edgarkech/scalable_field_camera/pictures/first_prototype/fomapan_200_4x5_2020-04-05-0008.jpg

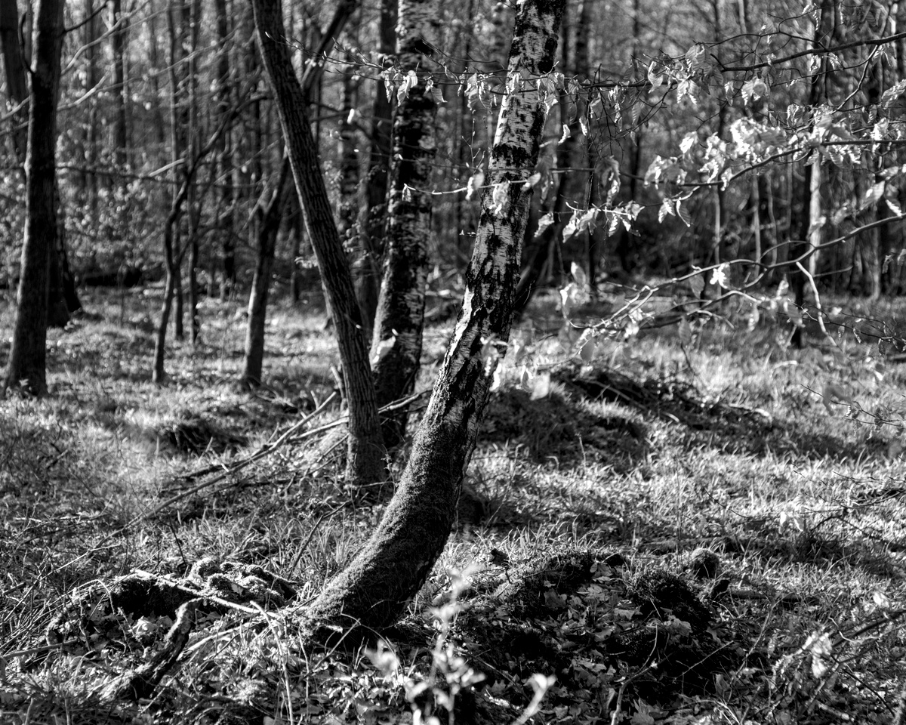
pictures/first_prototype/fomapan_200_4x5_2020-04-05-0008.jpg
