edgarkech/scalable_field_camera/pictures/first_prototype/MVIMG_20200405_085028_163_01.jpg

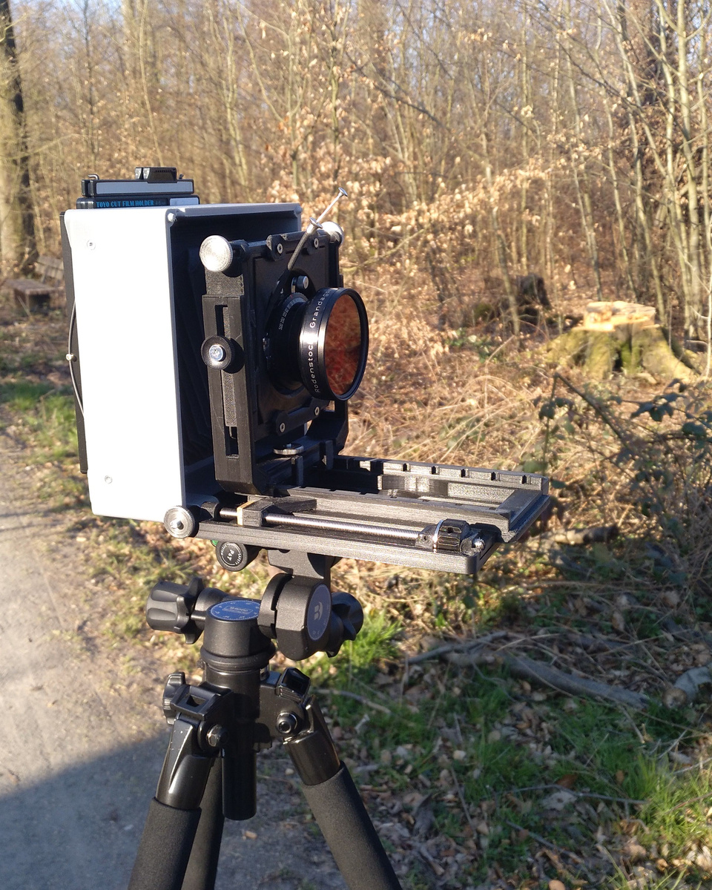
pictures/first_prototype/MVIMG_20200405_085028_163_01.jpg
