edgarkech/scalable_field_camera/pictures/first_prototype/MVIMG_20200405_091932_636.jpg

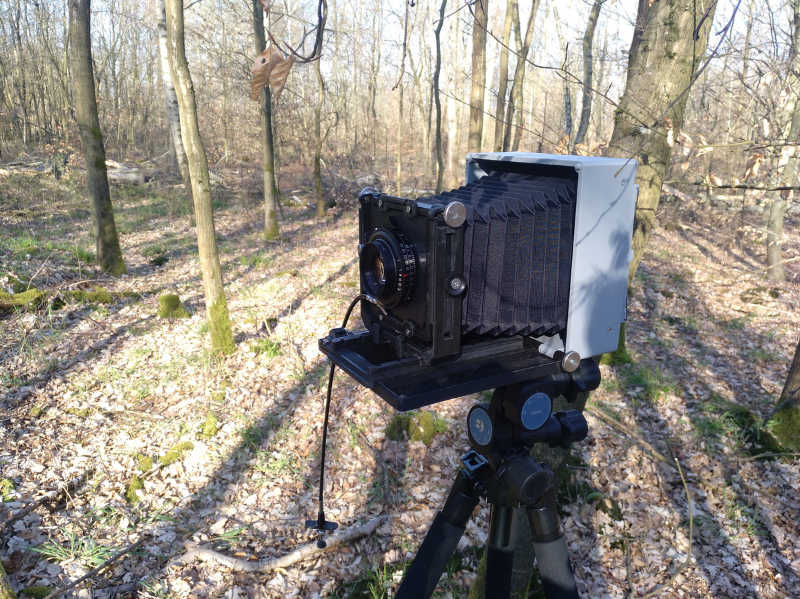
pictures/first_prototype/MVIMG_20200405_091932_636.jpg
