edgarkech/scalable_field_camera/pictures/version_1.0/IMG_20250819_194735843_HDR.jpg

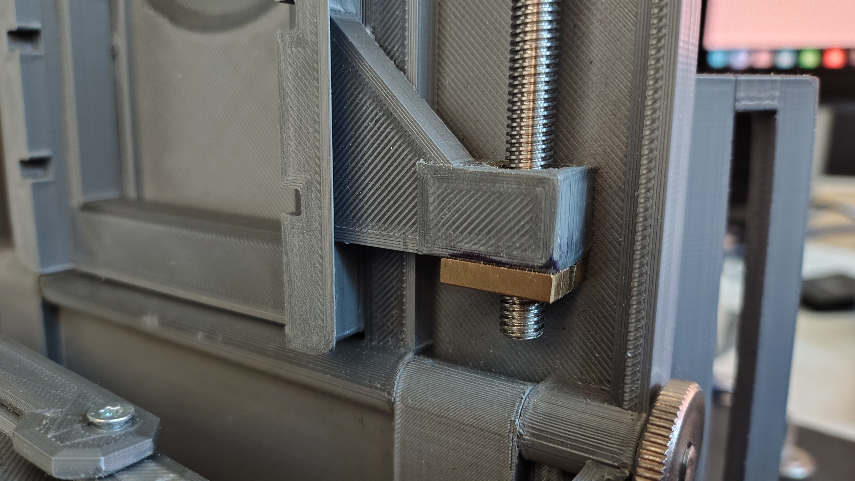
pictures/version_1.0/IMG_20250819_194735843_HDR.jpg
