edgarkech/scalable_field_camera/pictures/version_1.0/IMG_20250819_194852616_HDR.jpg

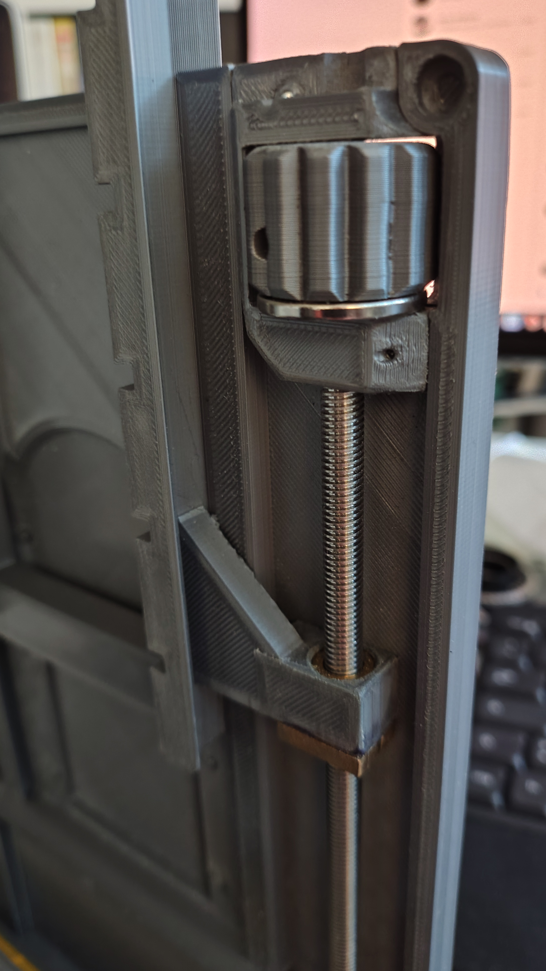
pictures/version_1.0/IMG_20250819_194852616_HDR.jpg
