edgarkech/scalable_field_camera/pictures/version_1.0/XT203508.jpg

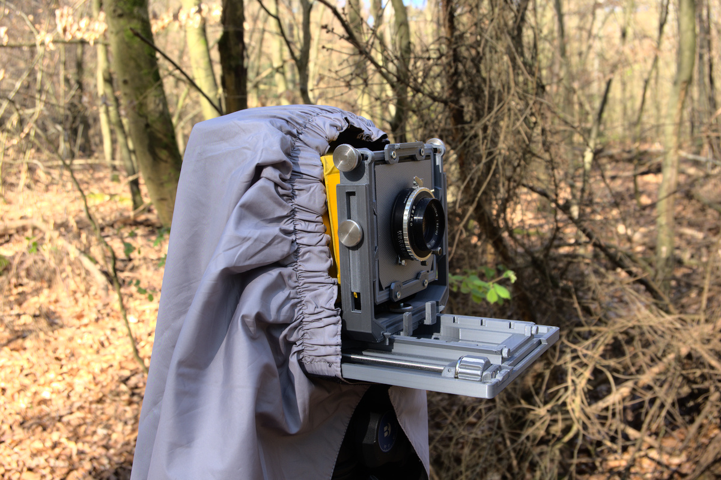
pictures/version_1.0/XT203508.jpg
