edgarkech/scalable_field_camera/pictures/version_1.0/XT203509.jpg

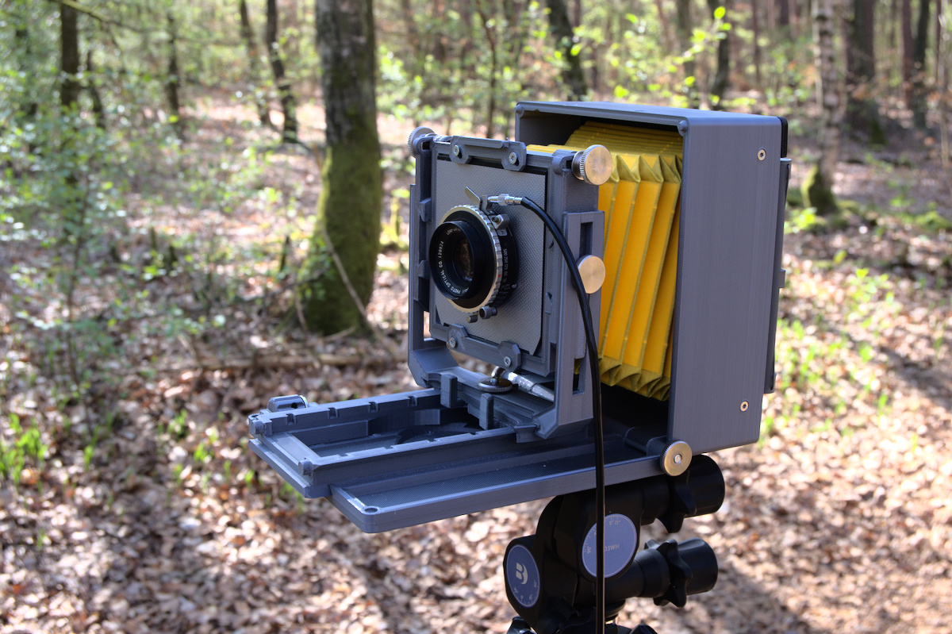
pictures/version_1.0/XT203509.jpg
