edgarkech/scalable_field_camera/pictures/version_1.0/XT203510.jpg

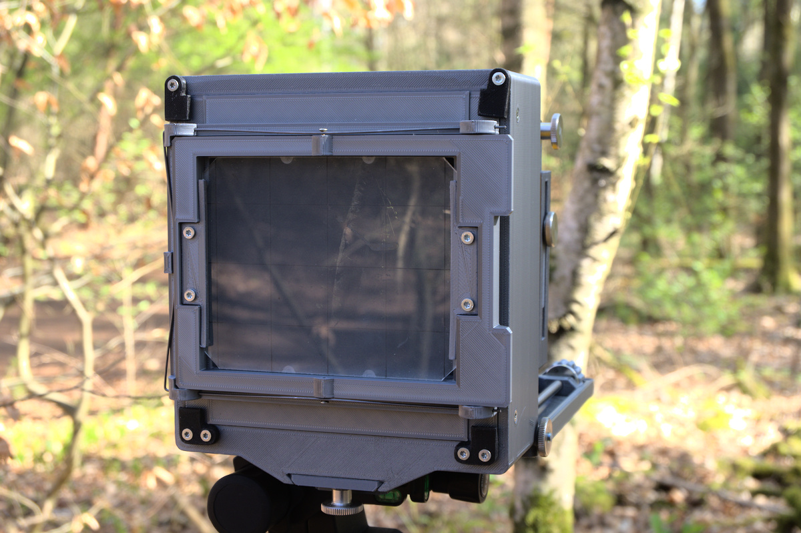
pictures/version_1.0/XT203510.jpg
