edgarkech/scalable_field_camera/pictures/XT203534.jpg

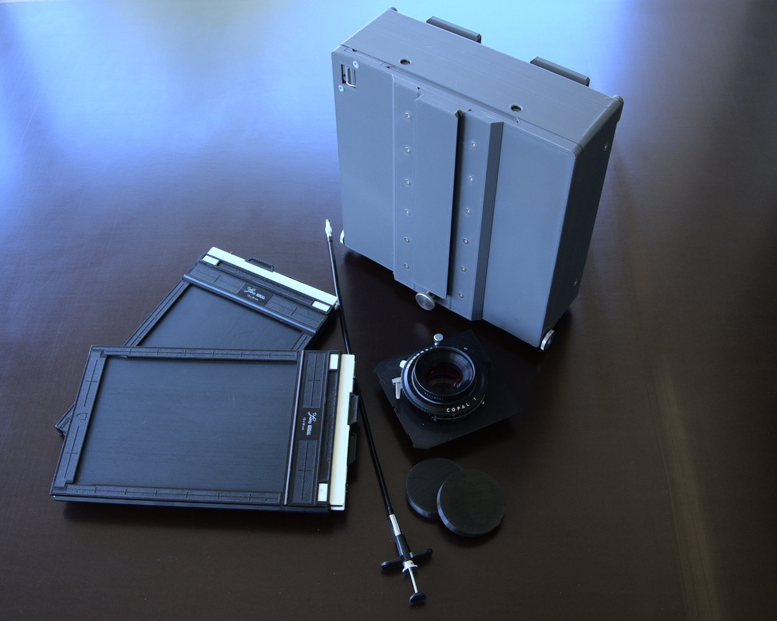
pictures/XT203534.jpg
