edgarkech/scalable_field_camera/pictures/XT203535.jpg

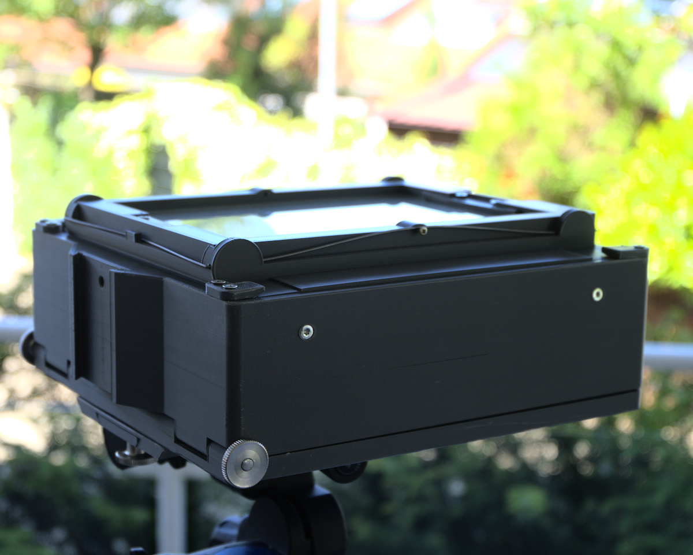
pictures/XT203535.jpg
