edgarkech/scalable_field_camera/pictures/XT203537.jpg

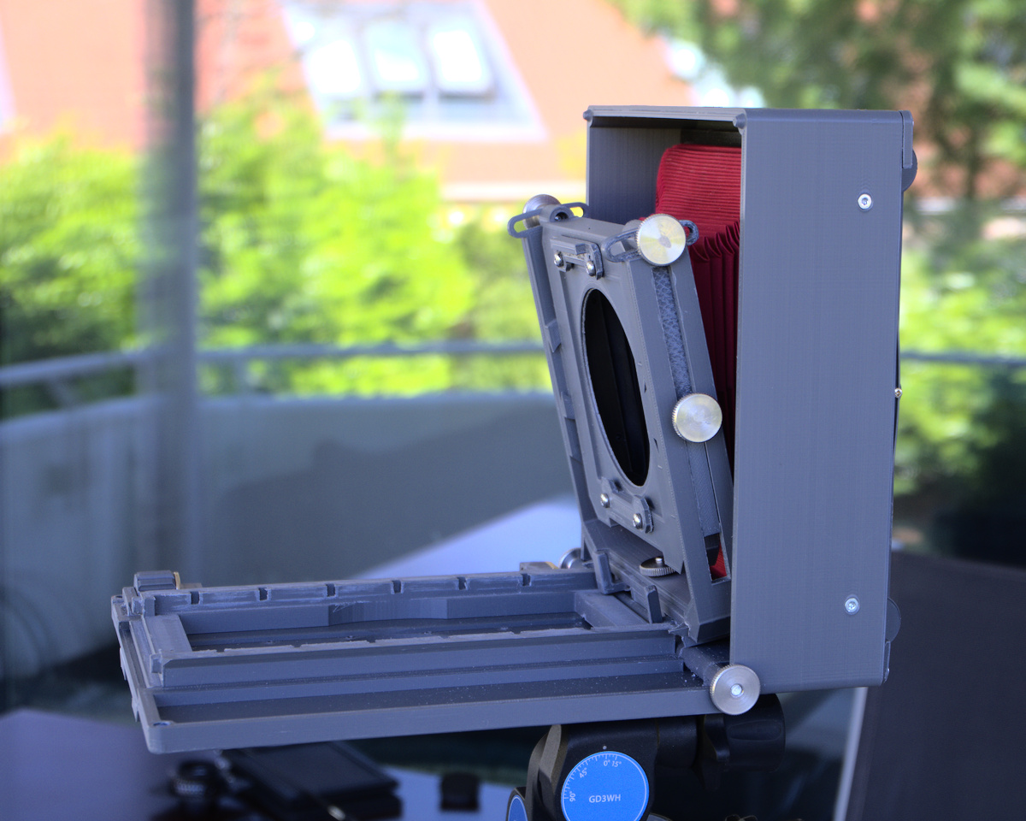
pictures/XT203537.jpg
