edgarkech/scalable_field_camera/pictures/XT203543.jpg

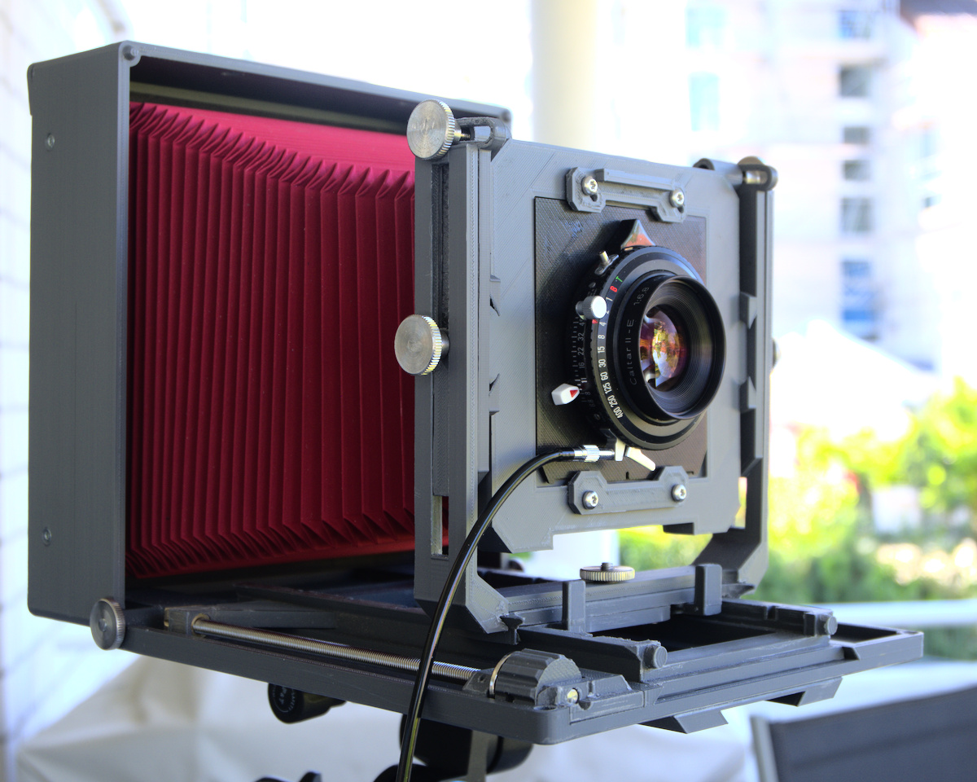
pictures/XT203543.jpg
