edgarkech/scalable_field_camera/pictures/XT203546.jpg

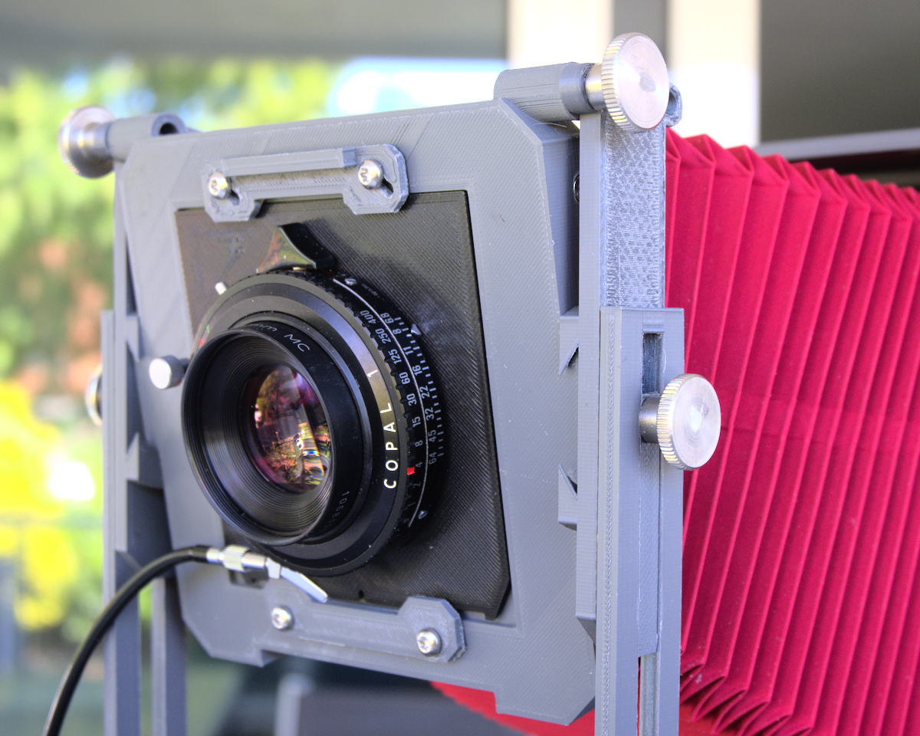
pictures/XT203546.jpg
