edgarkech/scalable_field_camera/STL_4x5/front_standard_tilt_plate.stl

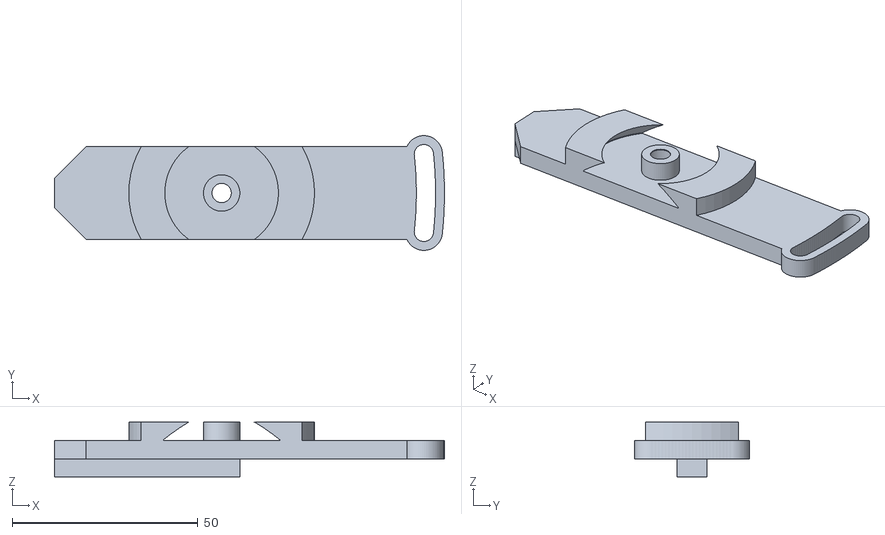
[picture p39: CAD file, 2020-03-26]
STL_4x5/front_standard_tilt_plate.stl
105.0 x 30.9 x 14.8
