edgarkech/scalable_field_camera/STL_5x7/slider.stl

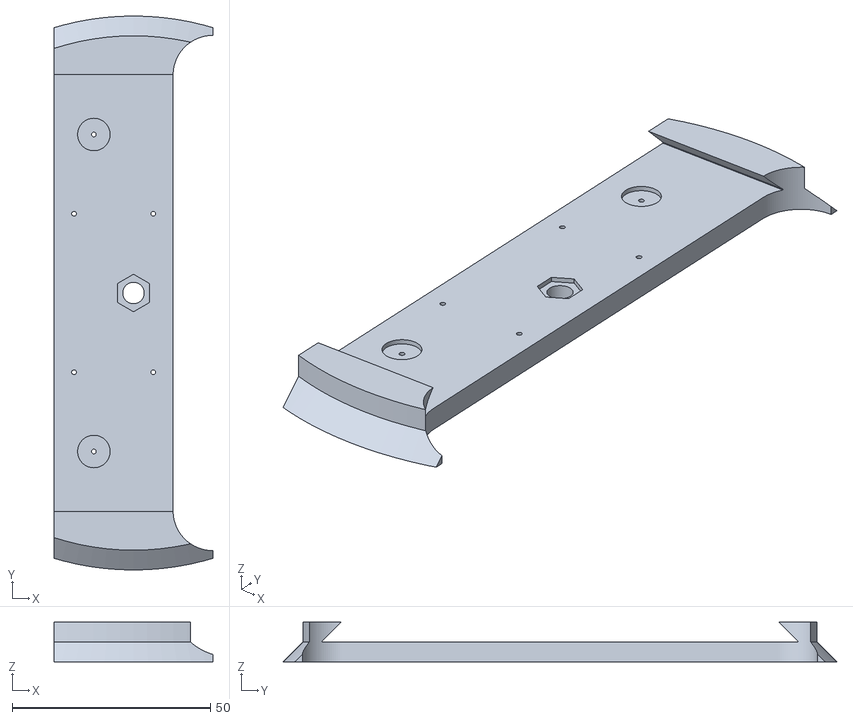
[picture p40: CAD file, 2020-05-10]
STL_5x7/slider.stl
40.0 x 139.8 x 10.0
