edgarkech/scalable_field_camera/STL_4x5/back_plate.stl

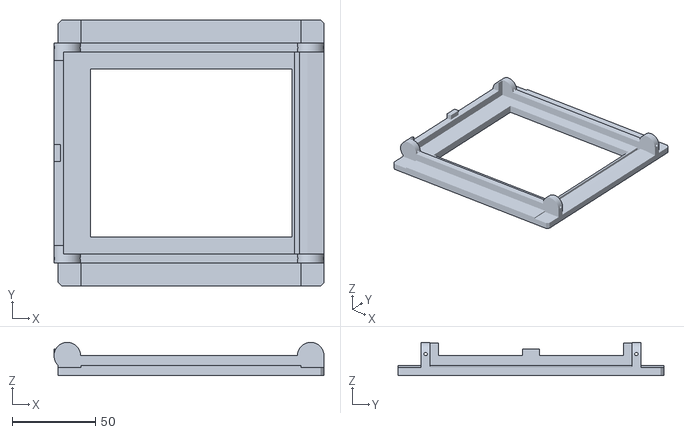
[picture p41: CAD file, 2020-03-26]
STL_4x5/back_plate.stl
162.1 x 159.6 x 20.0
