edgarkech/scalable_field_camera/STL_5x7/pulling_lever.stl

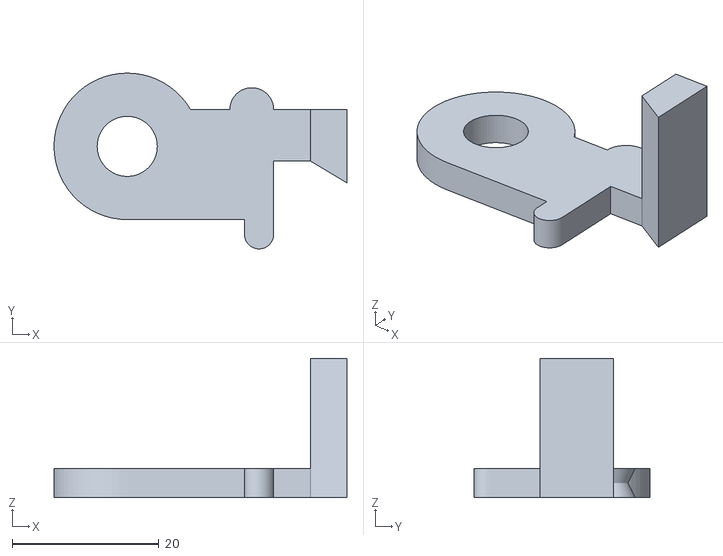
[picture p42: CAD file, 2020-05-10]
STL_5x7/pulling_lever.stl
40.0 x 24.0 x 19.0
