edgarkech/scalable_field_camera/STL_4x5/lensboard_carrier.stl

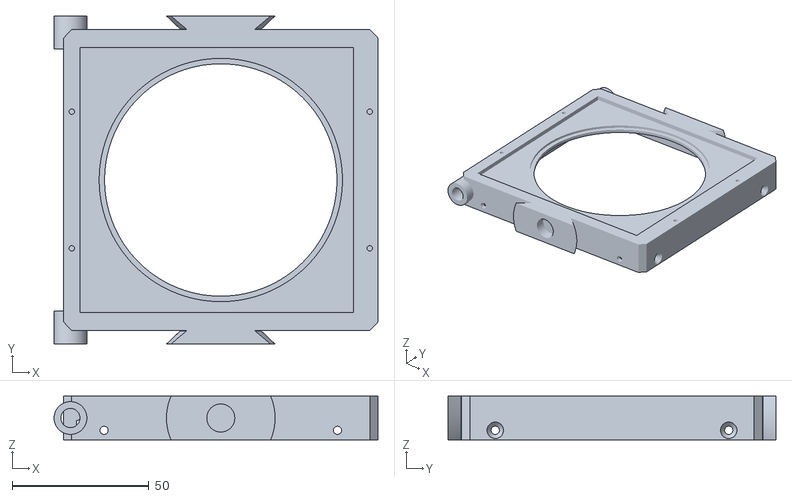
[picture p43: CAD file, 2020-03-26]
STL_4x5/lensboard_carrier.stl
118.5 x 120.0 x 16.0
