edgarkech/scalable_field_camera/STL_5x7/lensboard_carrier.stl

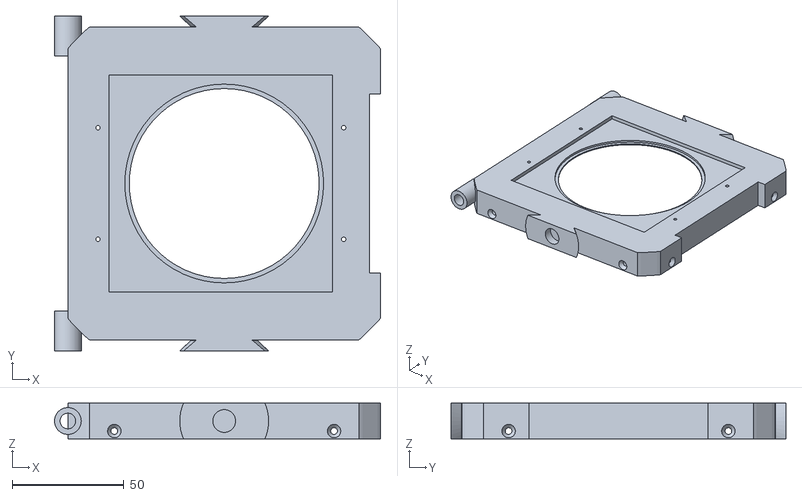
[picture p44: CAD file, 2020-05-10]
STL_5x7/lensboard_carrier.stl
146.0 x 150.0 x 16.0
