edgarkech/scalable_field_camera/STL_4x5/front_standard.stl

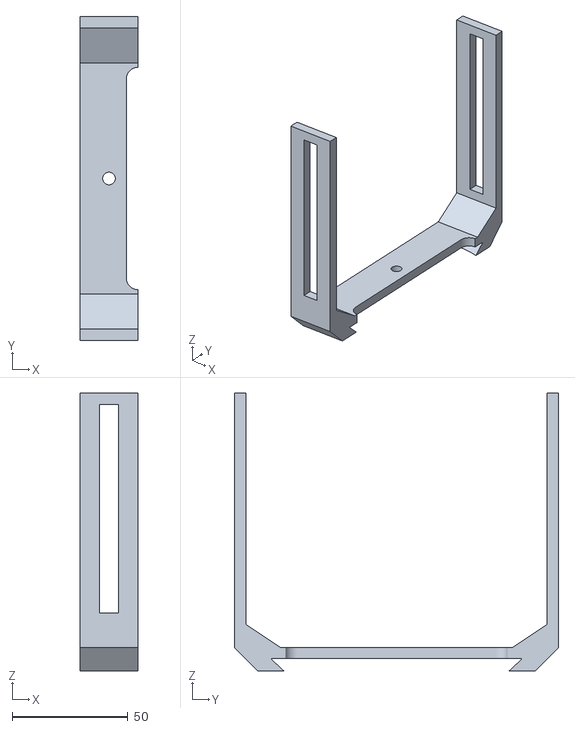
[picture p45: CAD file, 2020-03-26]
STL_4x5/front_standard.stl
25.0 x 140.0 x 120.0
