edgarkech/scalable_field_camera/STL_5x7/front_lid_dovetail.stl

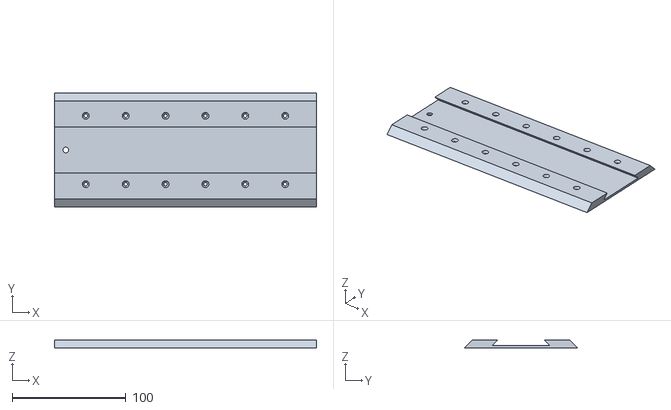
[picture p46: CAD file, 2020-05-06]
STL_5x7/front_lid_dovetail.stl
230.0 x 100.0 x 7.00
