edgarkech/scalable_field_camera/STL_4x5/ground_glass_frame.stl

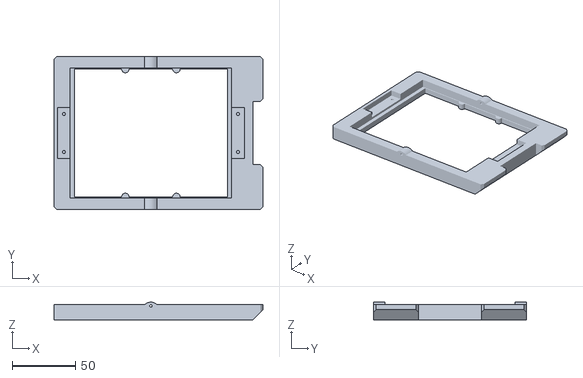
[picture p47: CAD file, 2020-03-26]
STL_4x5/ground_glass_frame.stl
165.0 x 120.5 x 14.0
