edgarkech/scalable_field_camera/STL_5x7/tripod_plate.stl

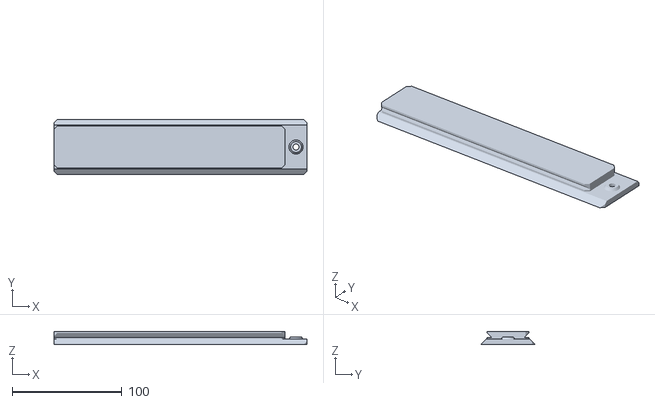
[picture p48: CAD file, 2020-05-06]
STL_5x7/tripod_plate.stl
230.0 x 49.8 x 12.0
