edgarkech/scalable_field_camera/STL_4x5/front_lid_dovetail.stl

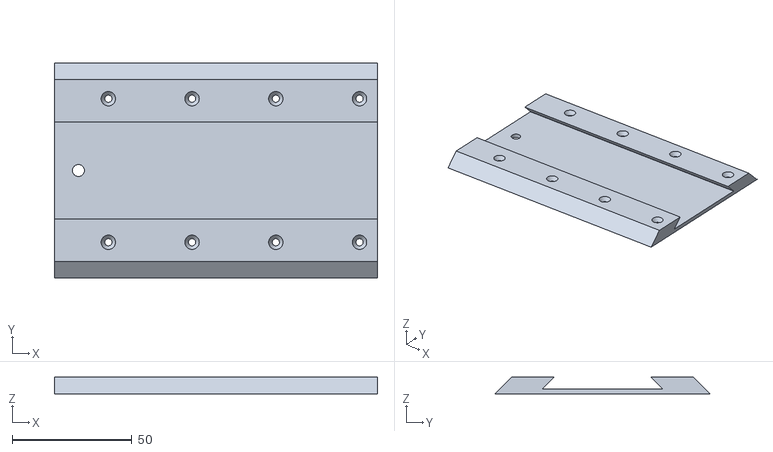
[picture p49: CAD file, 2020-03-26]
STL_4x5/front_lid_dovetail.stl
135.0 x 90.0 x 7.00
