edgarkech/scalable_field_camera/STL_5x7/ground_glass_frame.stl

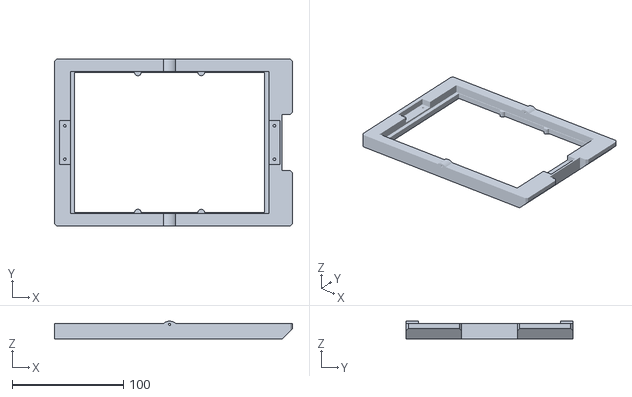
[picture p50: CAD file, 2020-05-06]
STL_5x7/ground_glass_frame.stl
214.0 x 150.0 x 16.0
