edgarkech/scalable_field_camera/STL_5x7/front_lid.stl

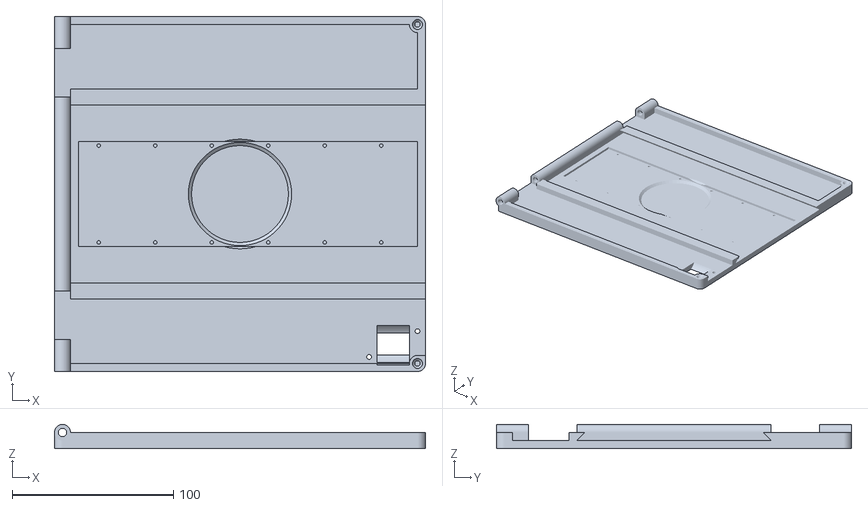
[picture p51: CAD file, 2020-04-23]
STL_5x7/front_lid.stl
230.0 x 220.0 x 15.0
