edgarkech/scalable_field_camera/STL_4x5/slider.stl

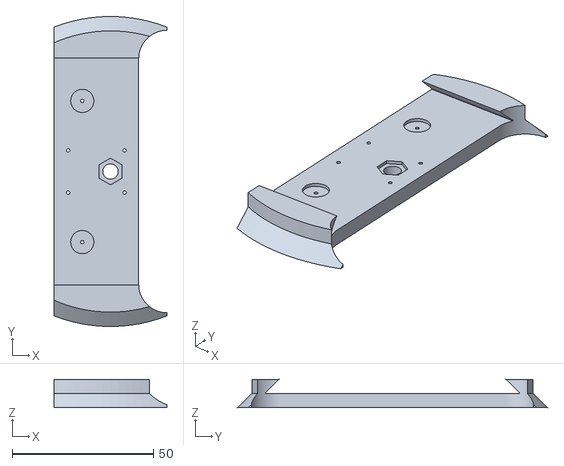
[picture p52: CAD file, 2020-03-26]
STL_4x5/slider.stl
40.0 x 109.8 x 10.0
