edgarkech/scalable_field_camera/STL_5x7/rails.stl

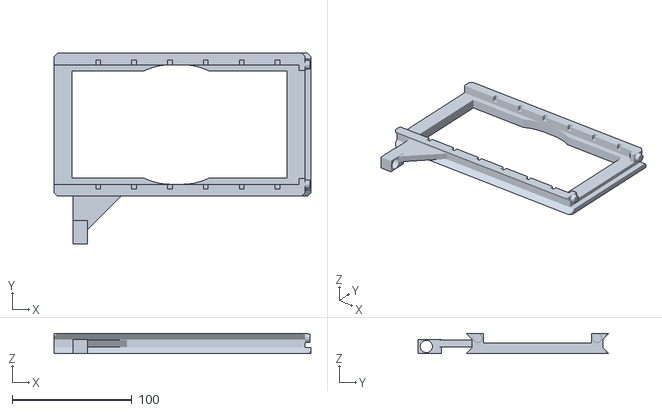
[picture p53: CAD file, 2020-04-23]
STL_5x7/rails.stl
215.0 x 159.9 x 17.0
