edgarkech/scalable_field_camera/STL_5x7/body.stl

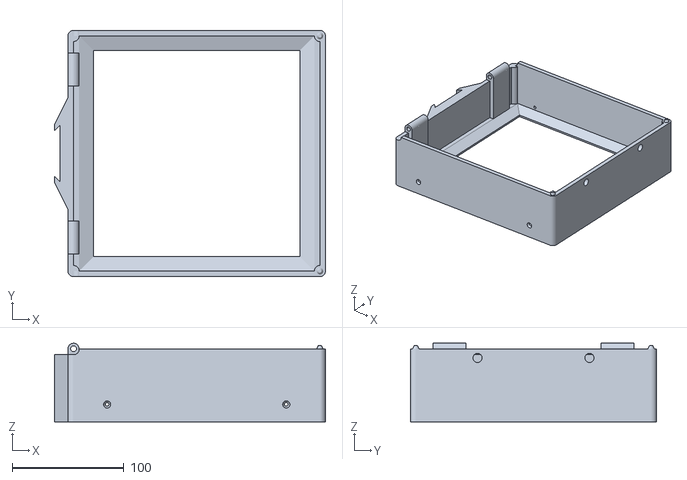
[picture p54: CAD file, 2020-04-23]
STL_5x7/body.stl
242.0 x 220.0 x 70.2
