edgarkech/scalable_field_camera/STL_5x7/bellows_front_frame.stl

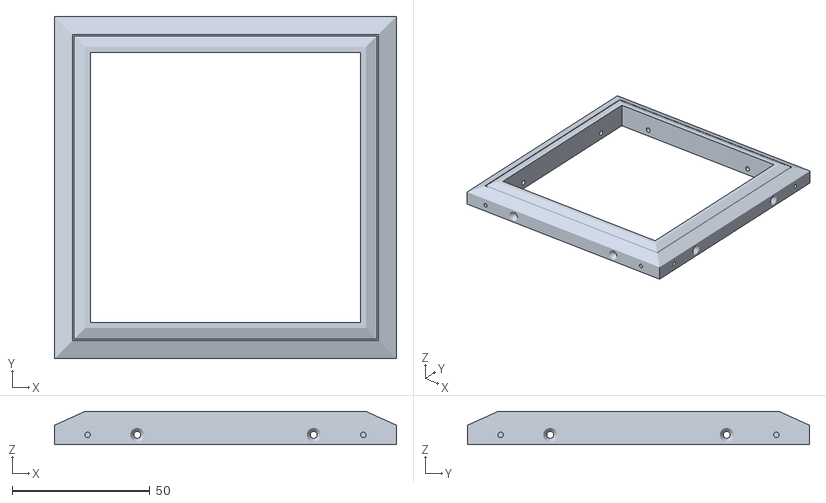
[picture p55: CAD file, 2020-04-22]
STL_5x7/bellows_front_frame.stl
124.0 x 124.0 x 12.0
