edgarkech/scalable_field_camera/STL_5x7/bellows_back_frame.stl

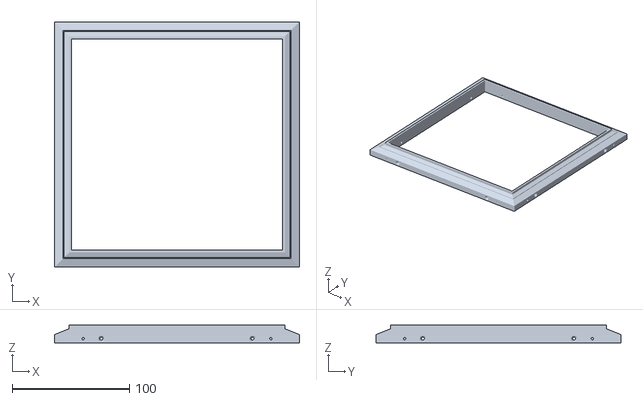
[picture p56: CAD file, 2020-04-22]
STL_5x7/bellows_back_frame.stl
209.0 x 209.0 x 15.0
