edgarkech/scalable_field_camera/STL_5x7/locking_lever.stl

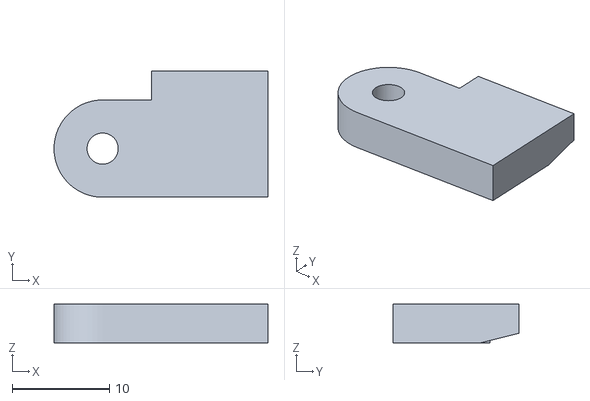
[picture p57: CAD file, 2020-03-26]
STL_5x7/locking_lever.stl
22.0 x 13.0 x 4.00
