edgarkech/scalable_field_camera/STL_5x7/lensboard_lower_clamp.stl

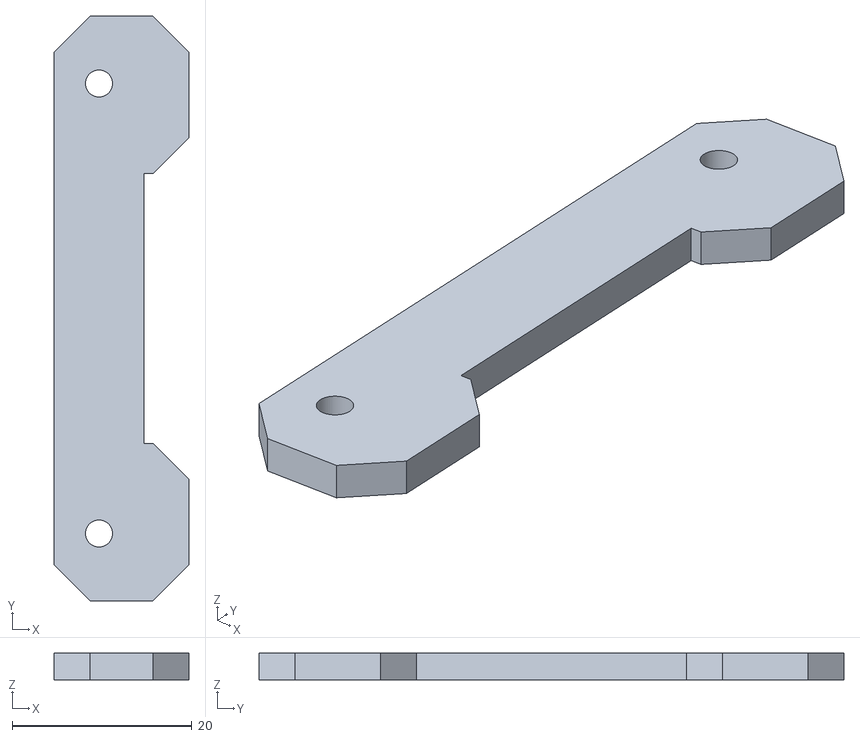
[picture p58: CAD file, 2020-03-26]
STL_5x7/lensboard_lower_clamp.stl
15.0 x 65.0 x 3.00
