edgarkech/scalable_field_camera/STL_5x7/locking_rail.stl

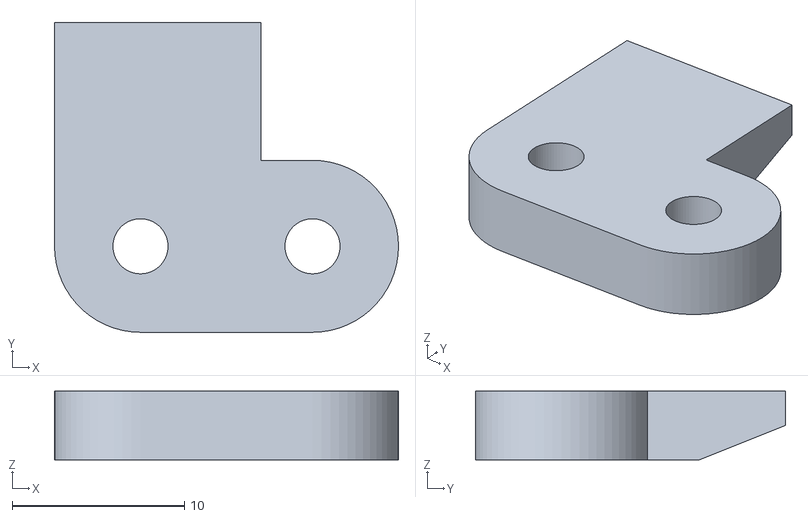
[picture p59: CAD file, 2020-03-26]
STL_5x7/locking_rail.stl
20.0 x 18.0 x 4.00
