edgarkech/scalable_field_camera/documentation/assembly/SFC_4x5_assembly (1).png

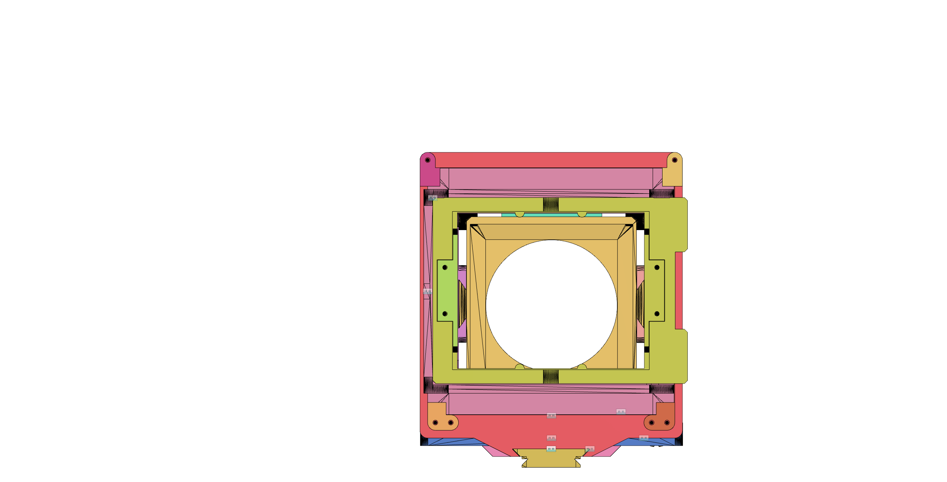
documentation/assembly/SFC_4x5_assembly (1).png
