edgarkech/scalable_field_camera/documentation/assembly/SFC_4x5_assembly (5).png

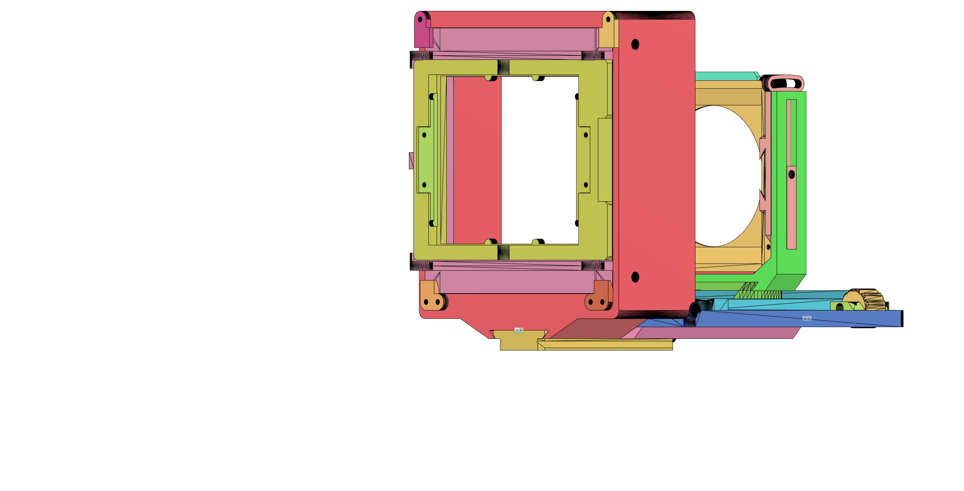
documentation/assembly/SFC_4x5_assembly (5).png
