edgarkech/scalable_field_camera/documentation/assembly/SFC_4x5_assembly (6).png

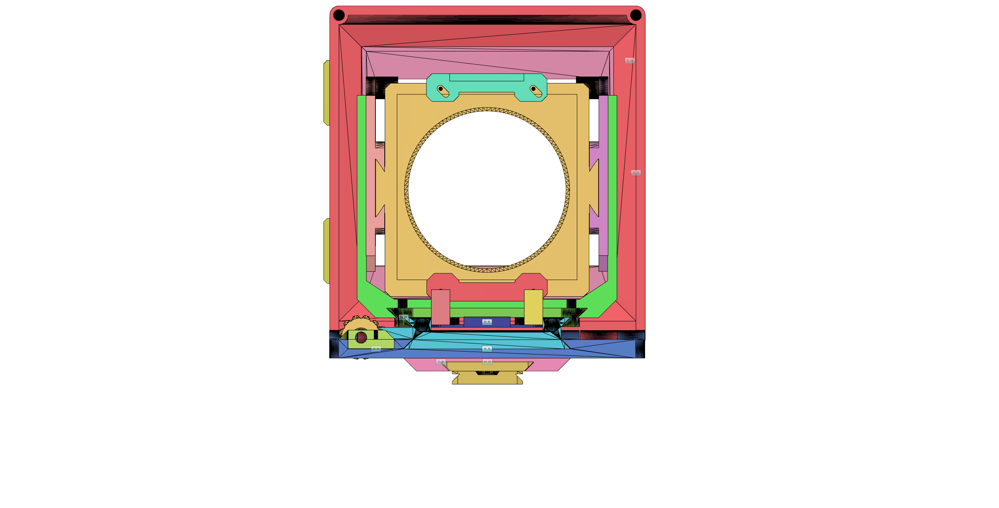
documentation/assembly/SFC_4x5_assembly (6).png
